JaimeMC7/TiltBot/Vision module/imagenes/black_binary_img.png

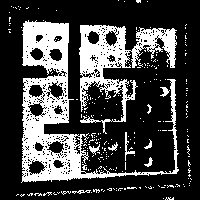
Vision module/imagenes/black_binary_img.png
