JaimeMC7/TiltBot/Vision module/imagenes/originales/desc.jpg

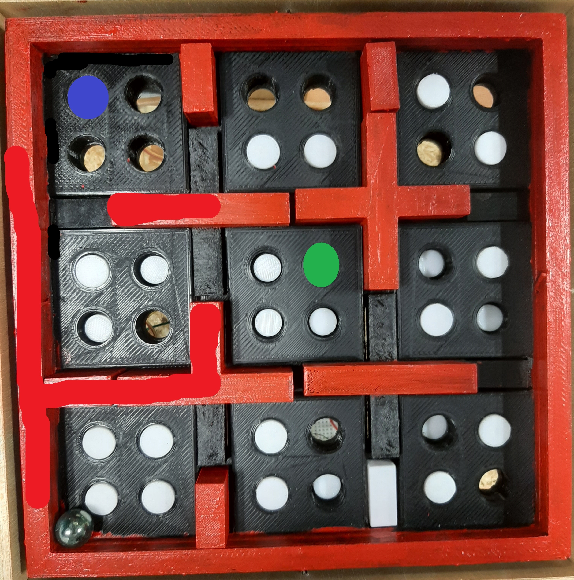
Vision module/imagenes/originales/desc.jpg
