JaimeMC7/TiltBot/Vision module/imagenes/originales/foto1.jpg

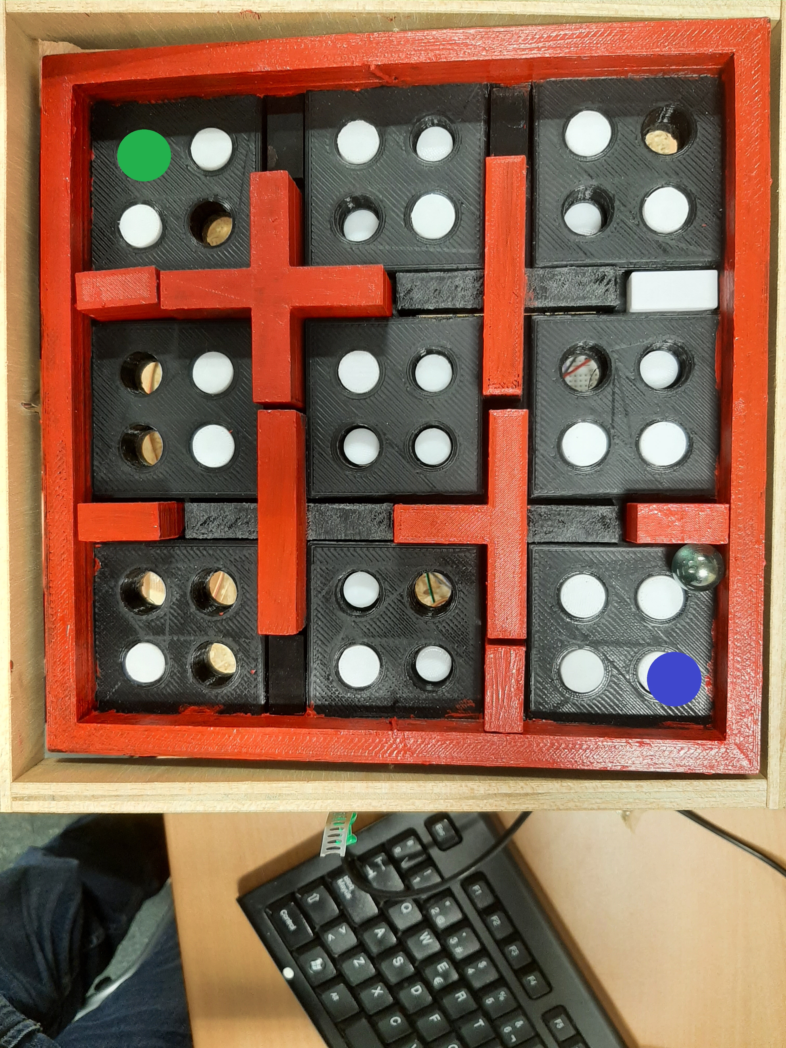
Vision module/imagenes/originales/foto1.jpg
