JaimeMC7/TiltBot/Vision module/imagenes/originales/foto9.jpg

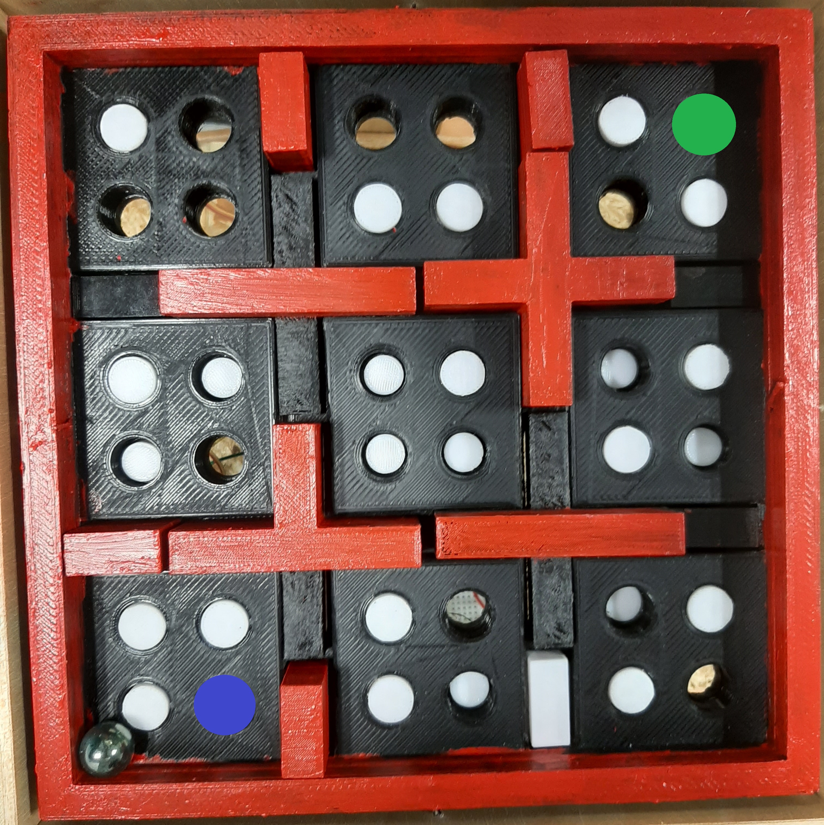
Vision module/imagenes/originales/foto9.jpg
