JaimeMC7/TiltBot/Vision module/imagenes/originales/foto10-org.jpg

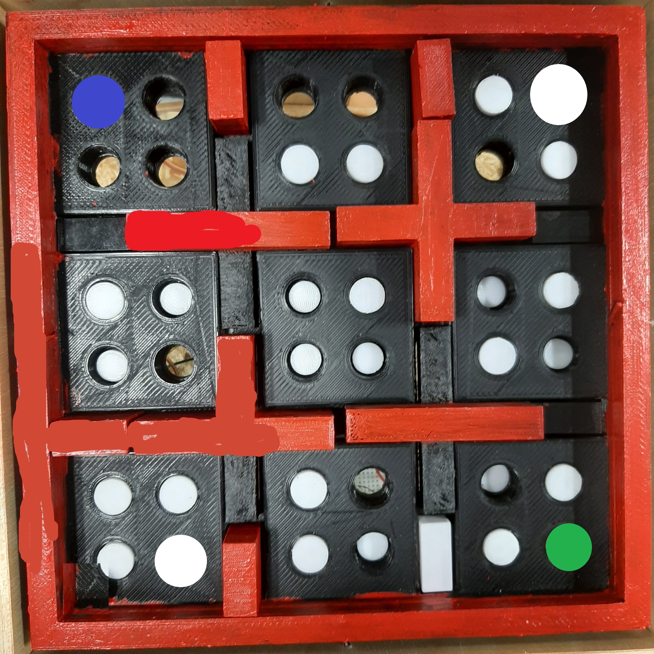
Vision module/imagenes/originales/foto10-org.jpg
