JaimeMC7/TiltBot/Vision module/imagenes/originales/foto10.jpg

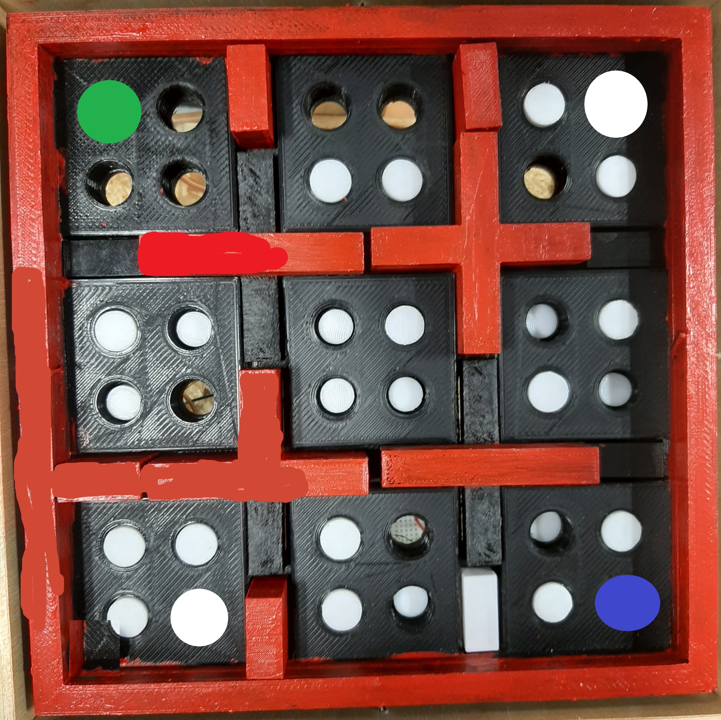
Vision module/imagenes/originales/foto10.jpg
