JaimeMC7/TiltBot/Vision module/imagenes/originales/foto11.jpg

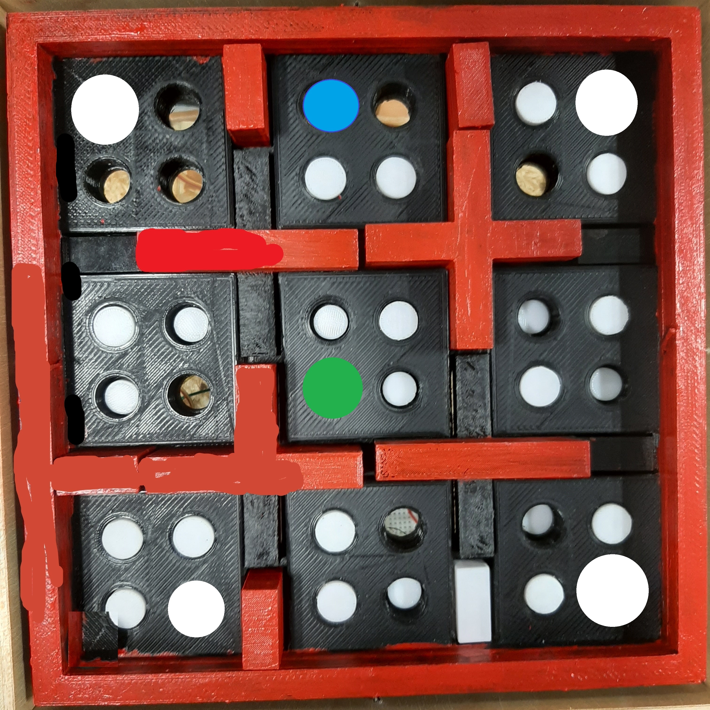
Vision module/imagenes/originales/foto11.jpg
