JaimeMC7/TiltBot/Vision module/imagenes/originales/foto15.jpg

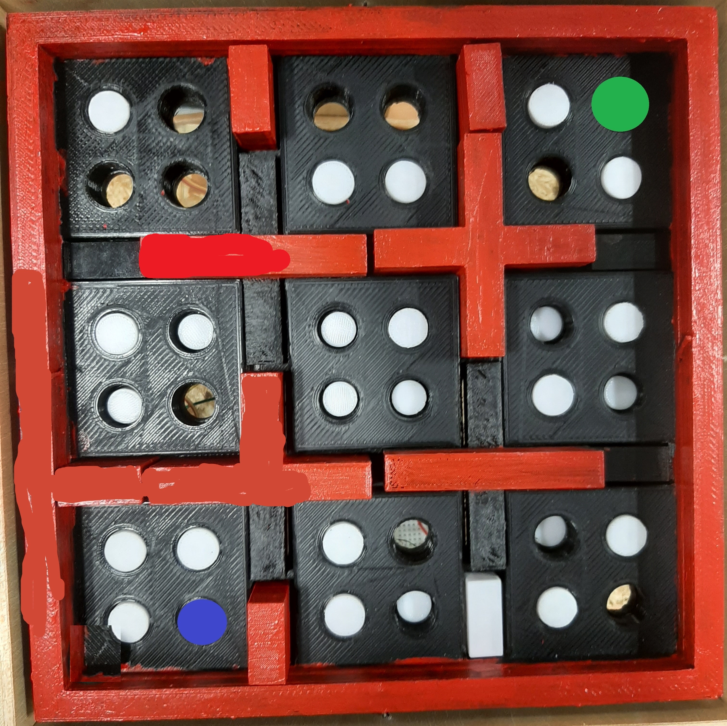
Vision module/imagenes/originales/foto15.jpg
