JaimeMC7/TiltBot/Vision module/imagenes/originales/foto21.jpg

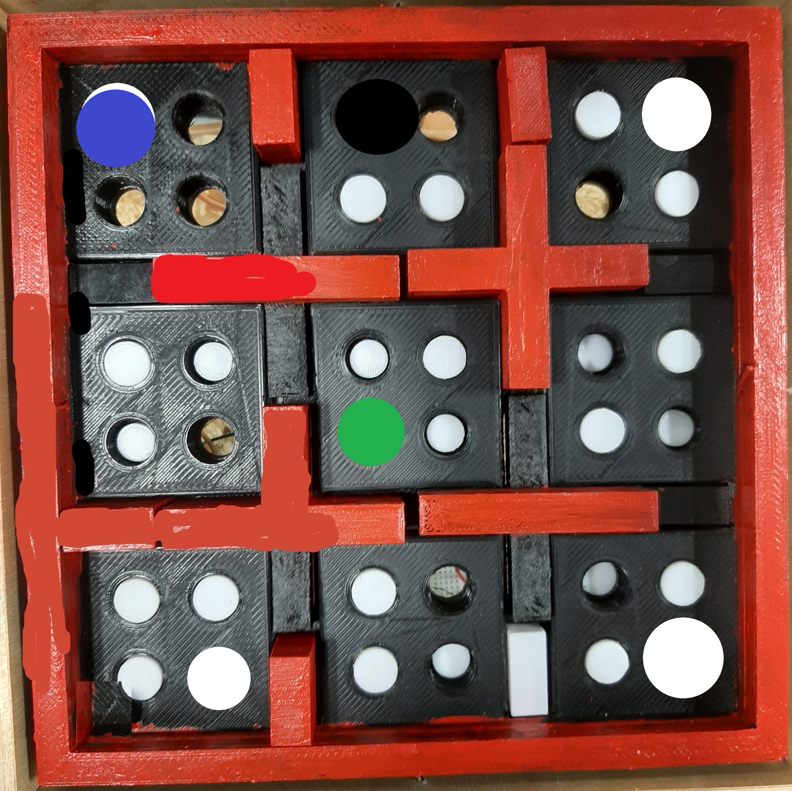
Vision module/imagenes/originales/foto21.jpg
