JaimeMC7/TiltBot/Vision module/imagenes/originales/img1.jpg

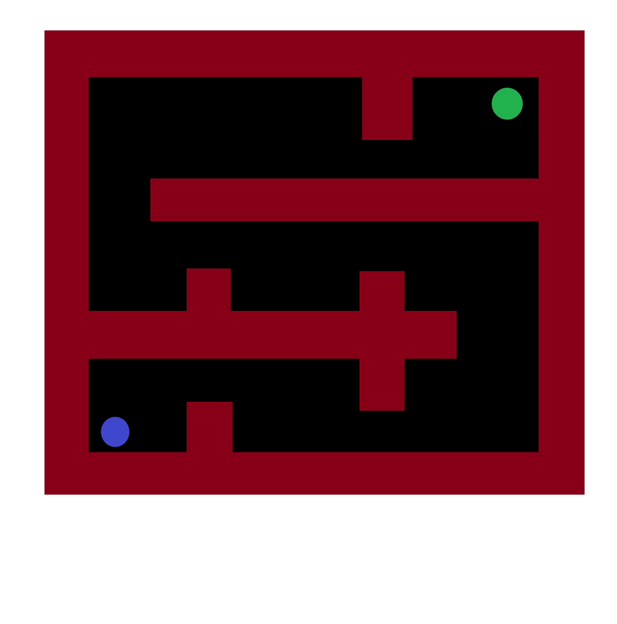
Vision module/imagenes/originales/img1.jpg
