JaimeMC7/TiltBot/Vision module/imagenes/originales/img.jpg

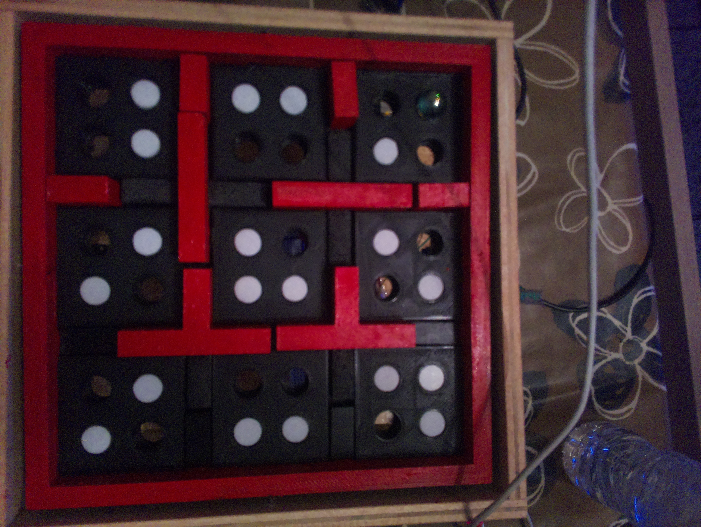
Vision module/imagenes/originales/img.jpg
