JaimeMC7/TiltBot/Vision module/imagenes/originales/Muros y esquinas.png

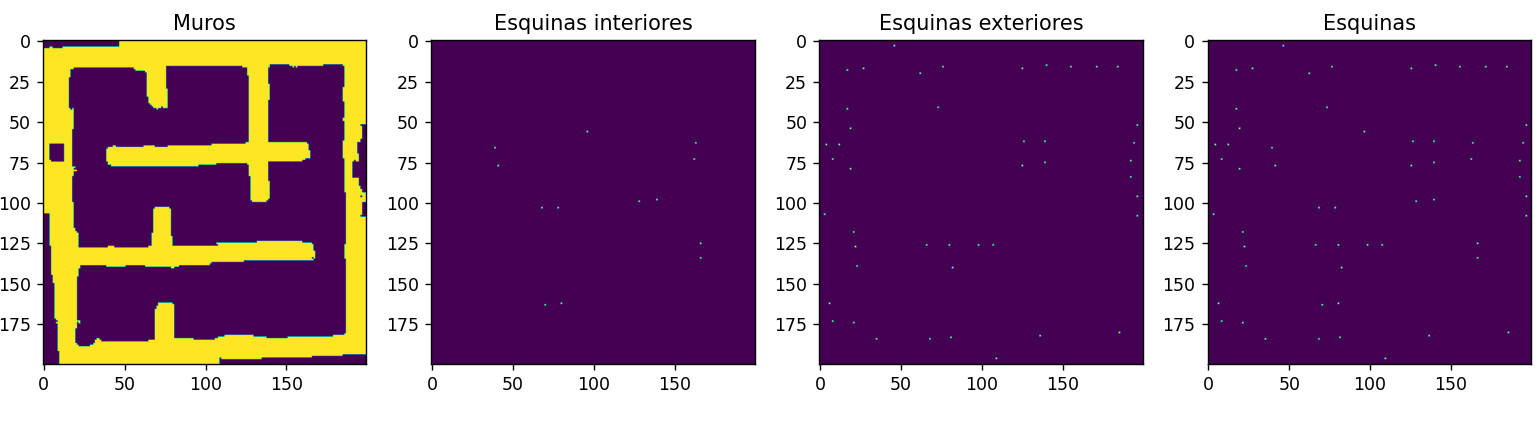
Vision module/imagenes/originales/Muros y esquinas.png
