JaimeMC7/TiltBot/Vision module/imagenes/r_gray_image.png

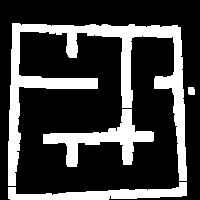
Vision module/imagenes/r_gray_image.png
