JaimeMC7/TiltBot/Vision module/imagenes/red_thick_zone.png

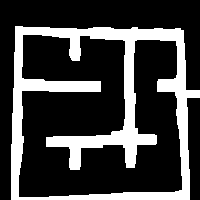
Vision module/imagenes/red_thick_zone.png
