JaimeMC7/TiltBot/Vision module/imagenes/red_zone_contourns.png

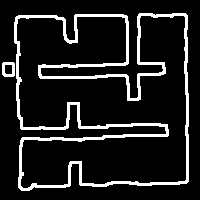
Vision module/imagenes/red_zone_contourns.png
