JaimeMC7/TiltBot/Vision module/imagenes/originales/prueba.jpg

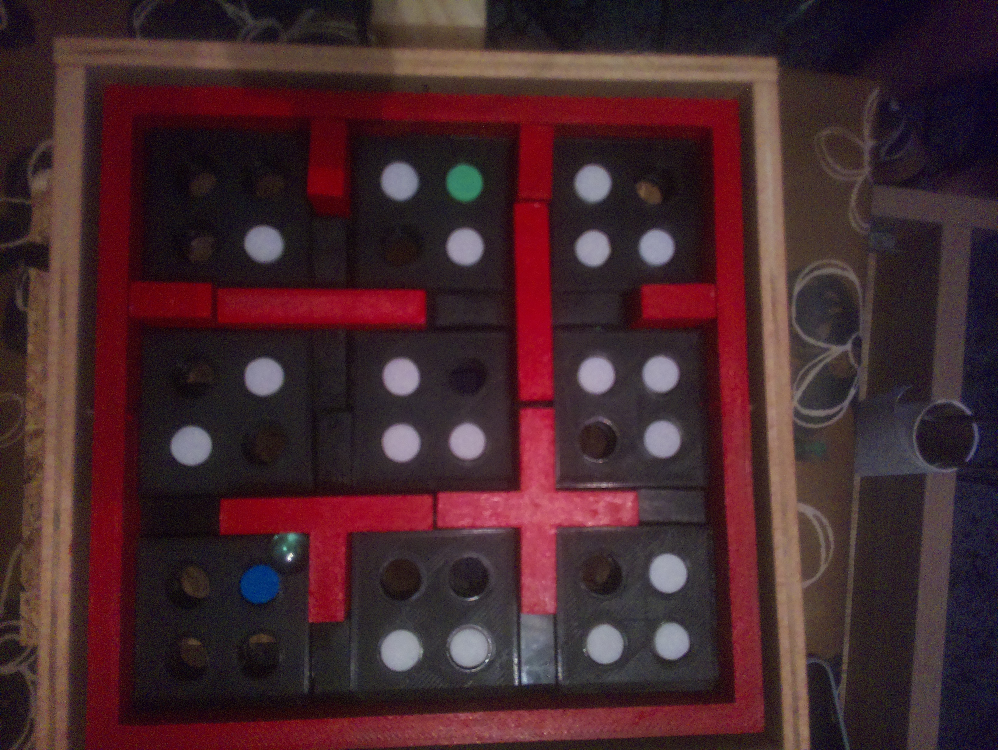
Vision module/imagenes/originales/prueba.jpg
