JaimeMC7/TiltBot/Vision module/Results/res-desc.png

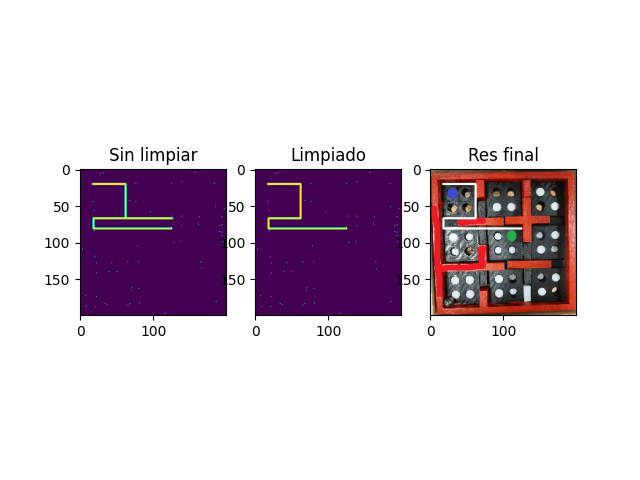
Vision module/Results/res-desc.png
