JaimeMC7/TiltBot/Vision module/Results/res-foto6.png

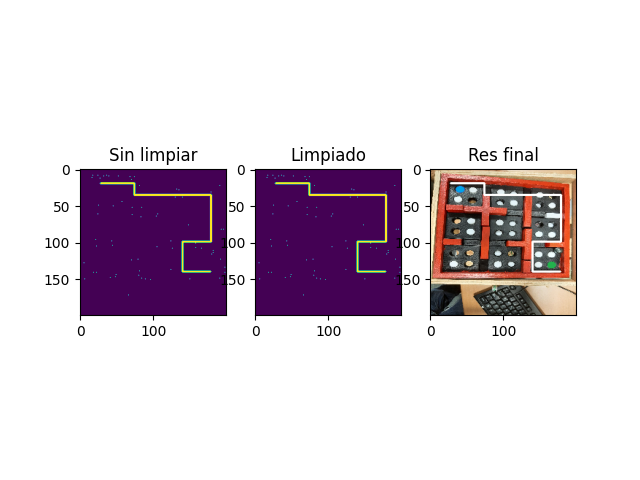
Vision module/Results/res-foto6.png
