JaimeMC7/TiltBot/Vision module/Results/Res-foto15 - post-clean.png

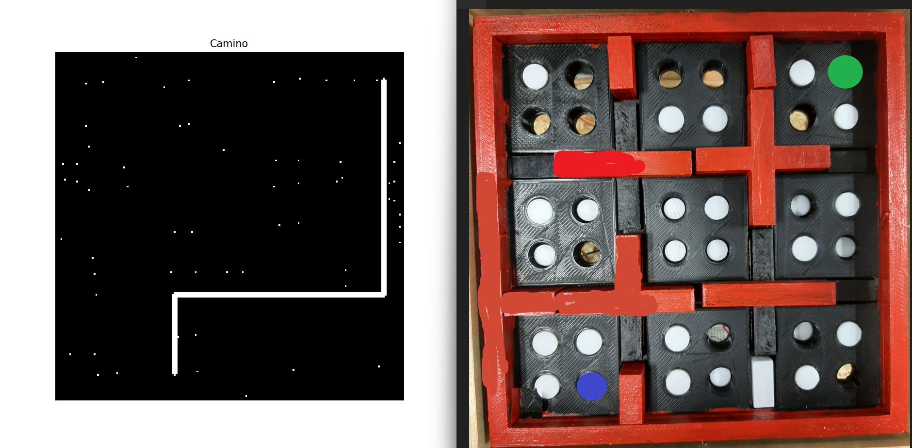
Vision module/Results/Res-foto15 - post-clean.png
