JaimeMC7/TiltBot/Vision module/Results/Res-foto16 - post-clean.png

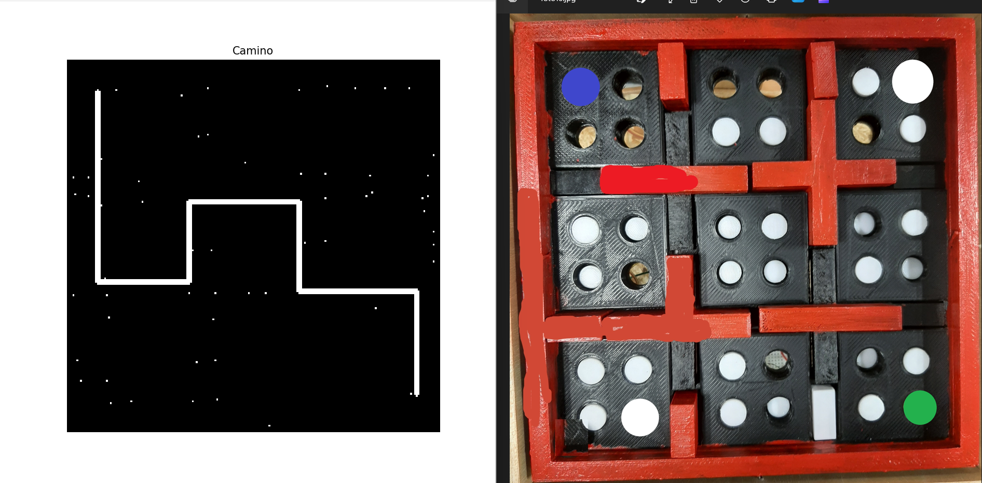
Vision module/Results/Res-foto16 - post-clean.png
