JaimeMC7/TiltBot/Vision module/Results/Res-foto17 - post-clean.png

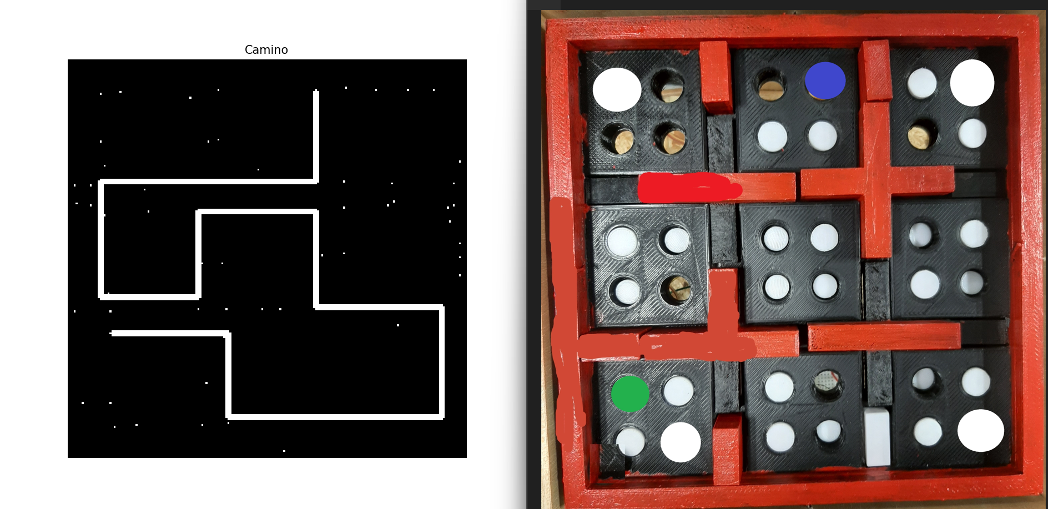
Vision module/Results/Res-foto17 - post-clean.png
