JaimeMC7/TiltBot/Vision module/imagenes/originales/foto3.jpg

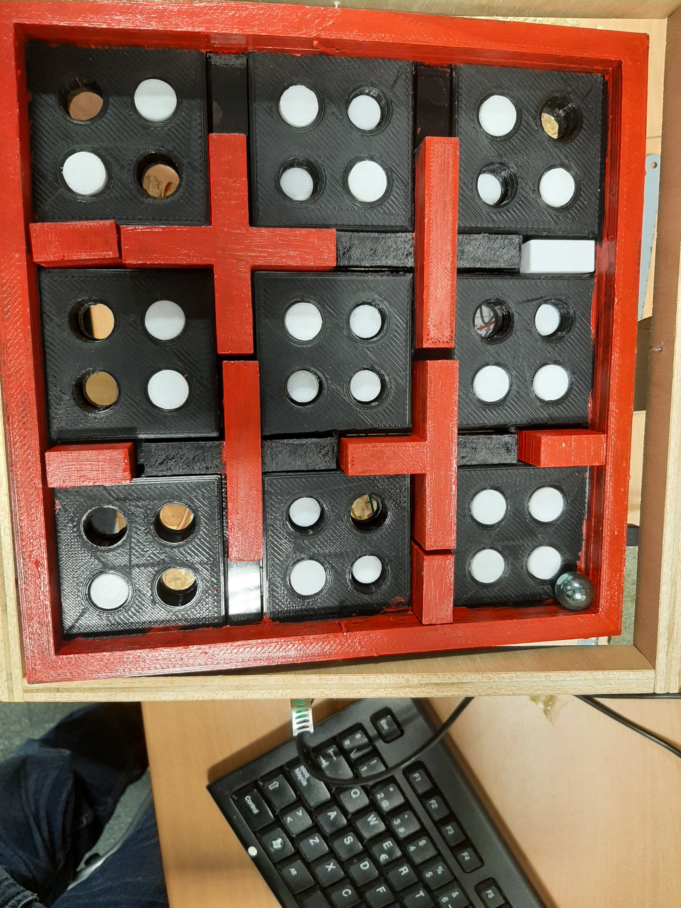
Vision module/imagenes/originales/foto3.jpg
