JaimeMC7/TiltBot/Vision module/imagenes/originales/foto5.jpg

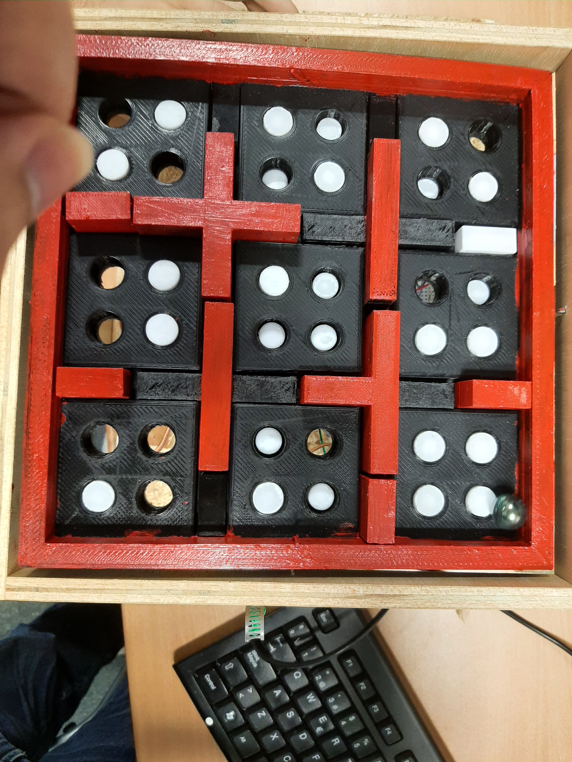
Vision module/imagenes/originales/foto5.jpg
