JaimeMC7/TiltBot/Vision module/imagenes/originales/foto7.jpg

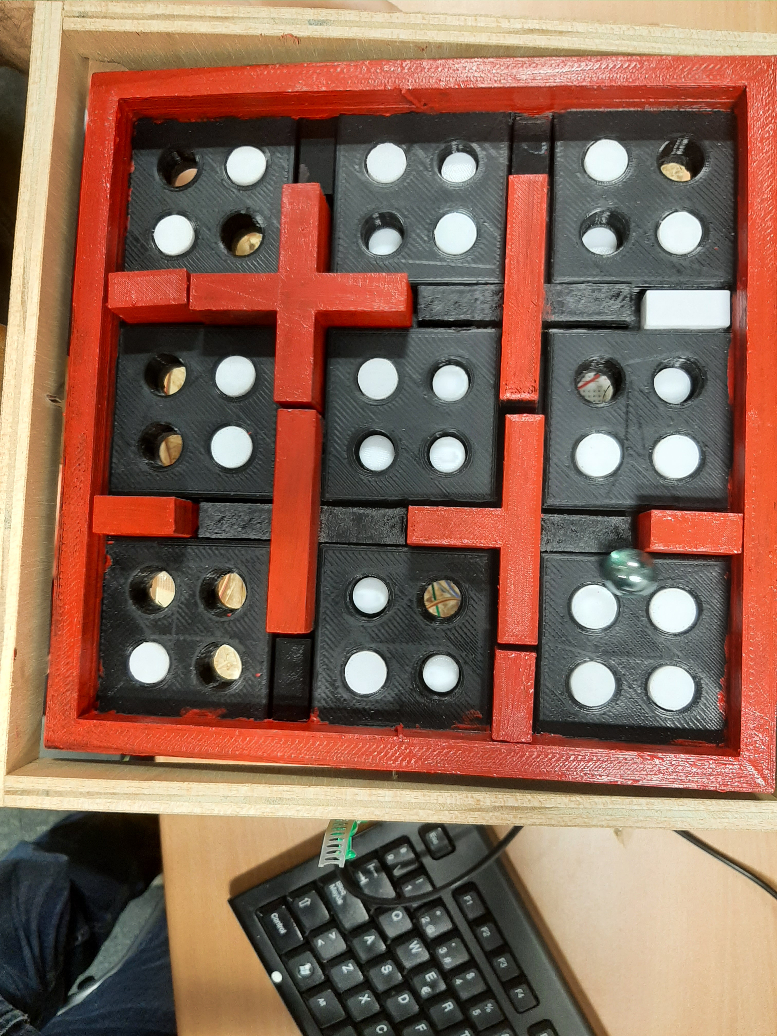
Vision module/imagenes/originales/foto7.jpg
