JaimeMC7/TiltBot/Vision module/imagenes/originales/foto8.jpg

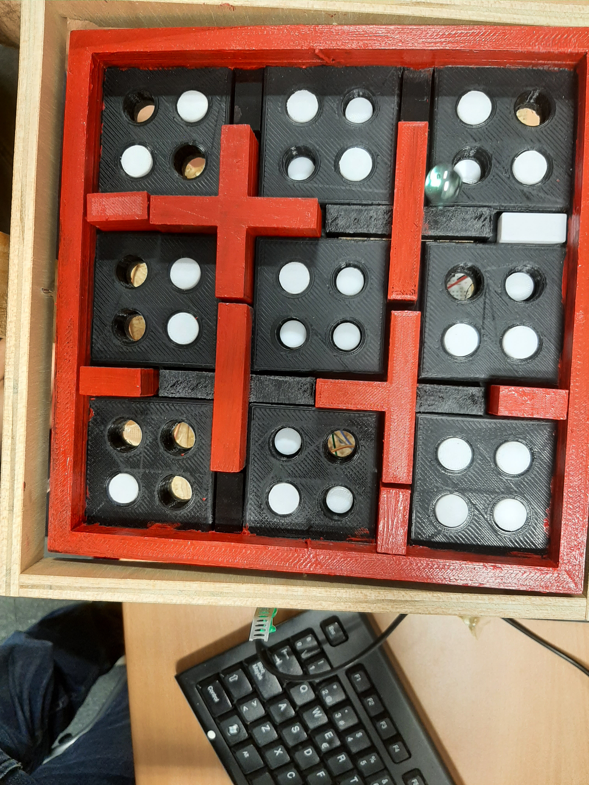
Vision module/imagenes/originales/foto8.jpg
